michaelerule/tinymarquee/graphics/DSCF3931.JPG

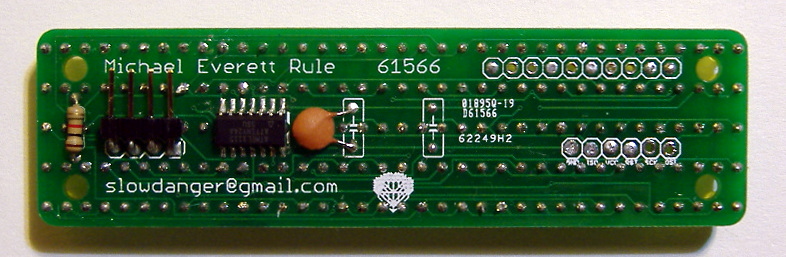
graphics/DSCF3931.JPG
