michaelerule/tinymarquee/serial communication/loop_to_serial.py

#!/usr/bin/env python
# -*- coding: utf-8 -*-
from __future__ import unicode_literals
import serial,os,sys,time,tty,termios
from pylab import *
import codecs

baudrate = 9600#4800
delay = .305

execfile('load_font.py')
execfile('getchar.py')
execfile('simpleserial.py')

gg = _Getch()

ser=startSerial(baudrate)

print('supported characters:')
print('  ',''.join(mapping))

message = "PaperMarquee 0.2       ♥♥♥        "
print('message is:')
print('  ',message)

try:
    while(1):
        for ch in message:
            sys.stdout.write(ch)
            sys.stdout.flush()
            if ch in mapping:
                index = mapping.index(ch)
                if index >=0 and index < len(chars):
                    chardata = chars[index]+[0,];
                    for column in chardata:    
                        ser.write(chr(column))
                        time.sleep(delay)
except:
    pass
finally:   
    closeSerial(ser)
