michaelerule/tinymarquee/serial communication/get_terminal_size.py

#!/usr/bin/env python
# -*- coding: utf-8 -*-


def getTerminalSize():
    '''
    get terminal dimension functions
    ripped from stackoverflow
    http://stackoverflow.com/questions/566746/how-to-get-console-window-width-in-python
    '''
    env = os.environ
    def ioctl_GWINSZ(fd):
        try:
            import fcntl, termios, struct, os
            cr = struct.unpack('hh', fcntl.ioctl(fd, termios.TIOCGWINSZ,'1234'))
        except:
            return
        return cr
    cr = ioctl_GWINSZ(0) or ioctl_GWINSZ(1) or ioctl_GWINSZ(2)
    if not cr:
        try:
            fd = os.open(os.ctermid(), os.O_RDONLY)
            cr = ioctl_GWINSZ(fd)
            os.close(fd)
        except:
            pass
    if not cr:
        cr = (env.get('LINES', 25), env.get('COLUMNS', 80))
    return int(cr[1]), int(cr[0])

(width, height) = getTerminalSize()
